Aemon777/chickies-robot/resources/3-d-files/major_parts/monitor mount lasercut v3.step

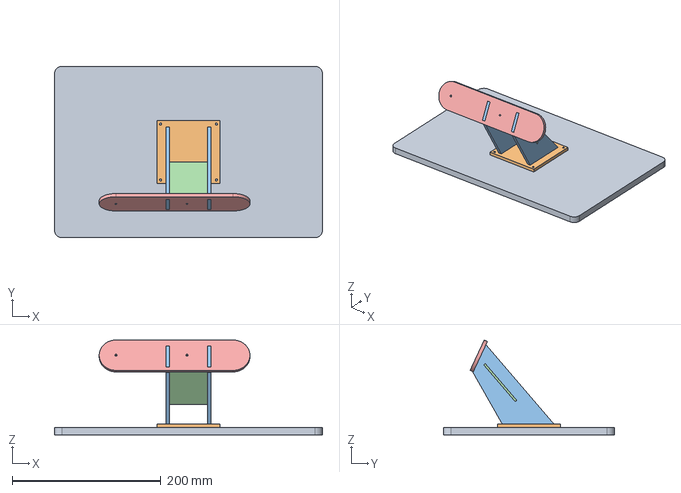
[picture p18: CAD file, 2022-01-21]
resources/3-d-files/major_parts/monitor mount lasercut v3.step
360.0 x 230.0 x 127.6 mm
