Aemon777/chickies-robot/resources/3-d-files/minor_parts/motorcontrollermount v1.step

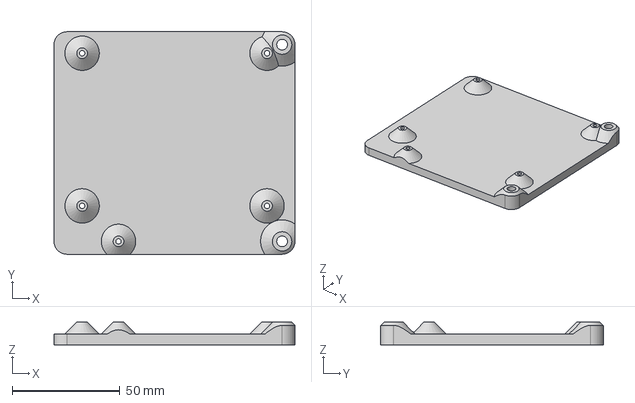
[picture p19: CAD file, 2022-01-21]
resources/3-d-files/minor_parts/motorcontrollermount v1.step
112.1 x 103.5 x 10.5 mm
