Aemon777/chickies-robot/resources/3-d-files/Arm_Models/ChickiesLogo.SLDPRT

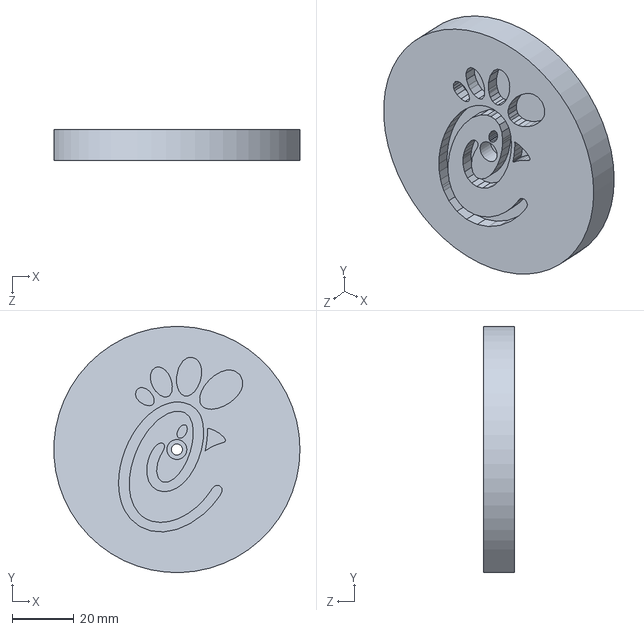
[picture p20: CAD file, 2022-03-17]
resources/3-d-files/Arm_Models/ChickiesLogo.SLDPRT
79.9 x 80.0 x 10.0 mm
