Aemon777/chickies-robot/resources/3-d-files/FCU-Part-Files/Anchor Left.SLDPRT

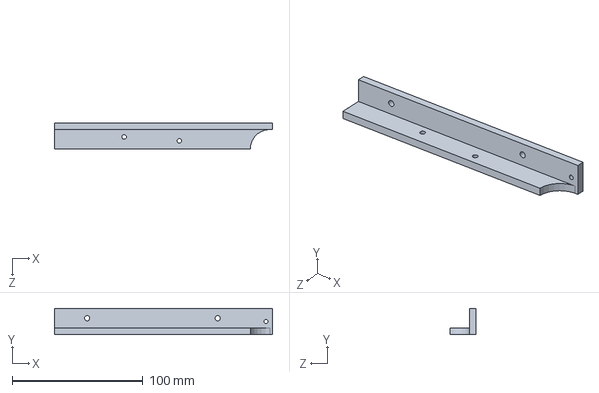
[picture p21: CAD file, 2022-03-31]
resources/3-d-files/FCU-Part-Files/Anchor Left.SLDPRT
167.0 x 20.0 x 20.0 mm
