Aemon777/chickies-robot/resources/3-d-files/minor_parts/powerboardmount v1.step

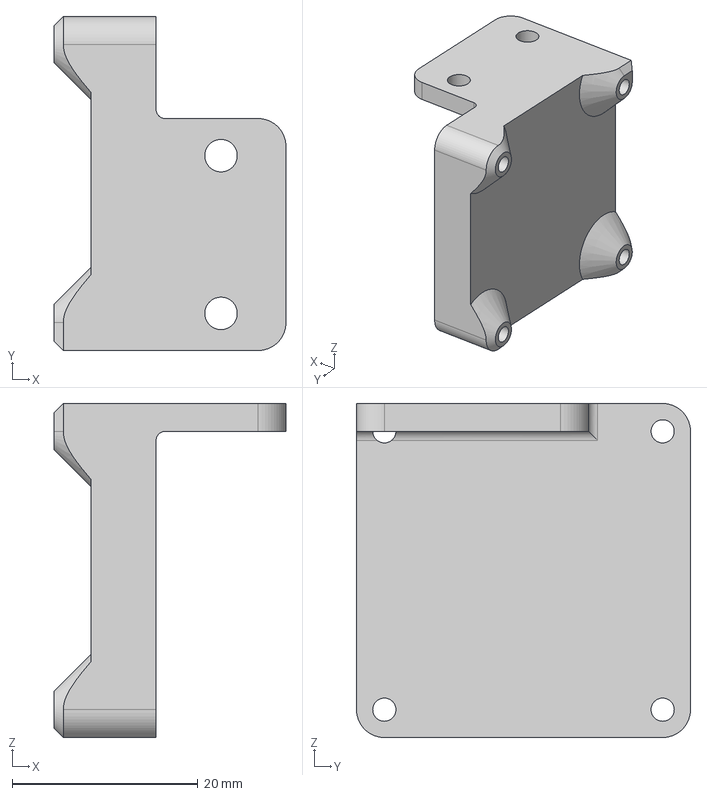
[picture p22: CAD file, 2022-01-21]
resources/3-d-files/minor_parts/powerboardmount v1.step
25.0 x 36.0 x 36.0 mm
