Aemon777/chickies-robot/resources/3-d-files/Arm_Models/Rack Extend.SLDPRT

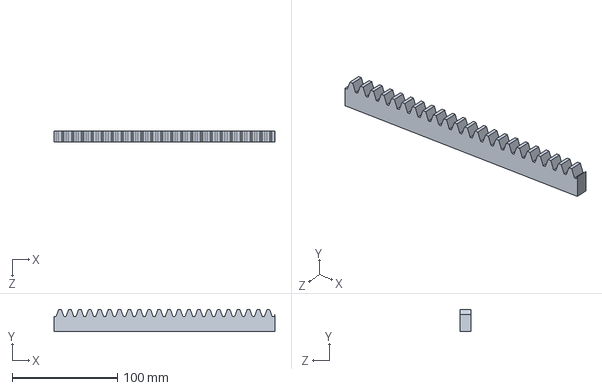
[picture p23: CAD file, 2022-03-17]
resources/3-d-files/Arm_Models/Rack Extend.SLDPRT
210.0 x 21.0 x 10.0 mm
