Aemon777/chickies-robot/resources/3-d-files/major_parts/lidarmount v7.step

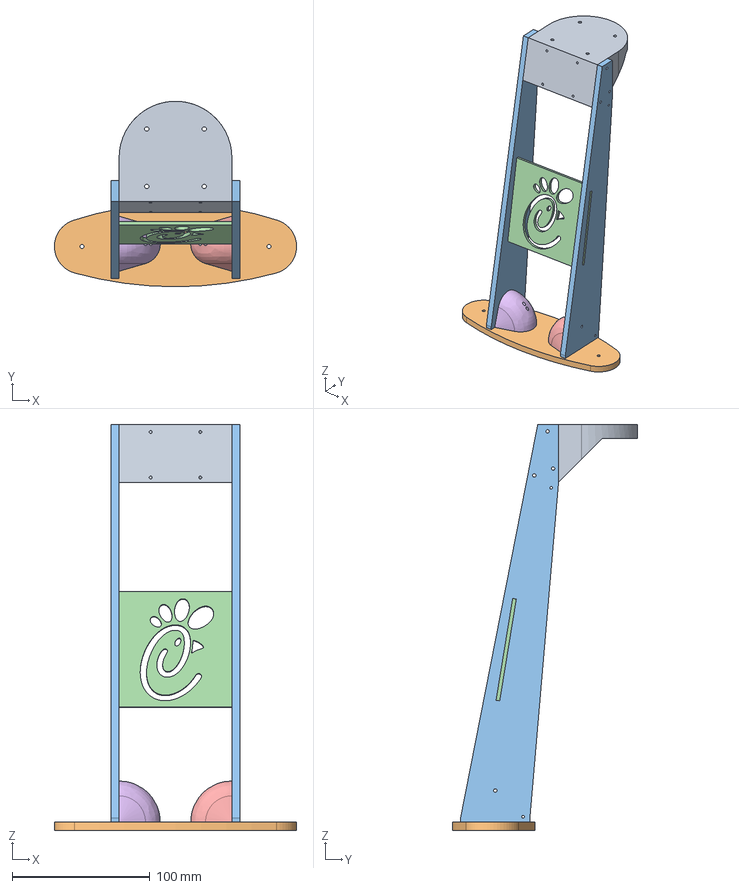
[picture p24: CAD file, 2022-01-21]
resources/3-d-files/major_parts/lidarmount v7.step
176.0 x 134.7 x 295.0 mm
