Aemon777/chickies-robot/resources/3-d-files/minor_parts/knob2 v1.step

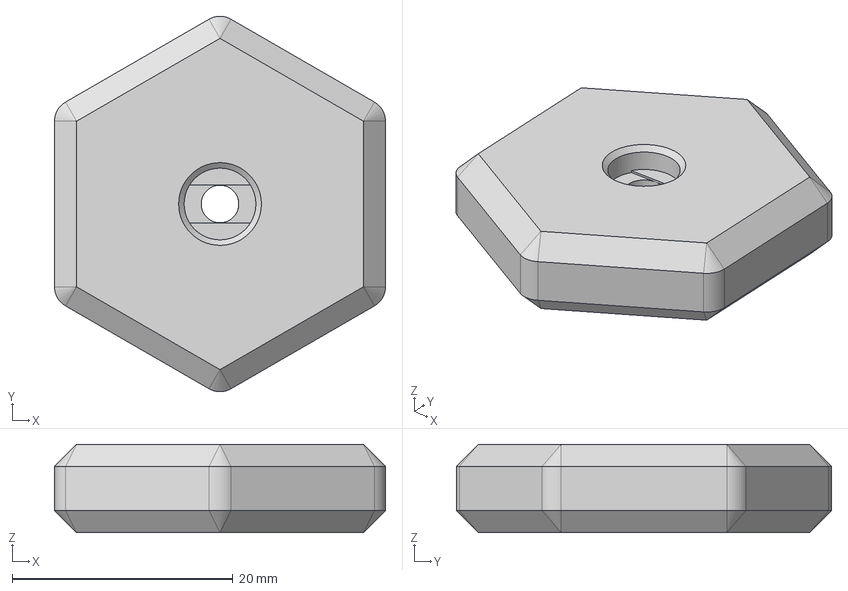
[picture p25: CAD file, 2022-01-21]
resources/3-d-files/minor_parts/knob2 v1.step
30.0 x 34.0 x 8.00 mm
