Aemon777/chickies-robot/resources/3-d-files/FCU-Part-Files/Bottom.SLDPRT

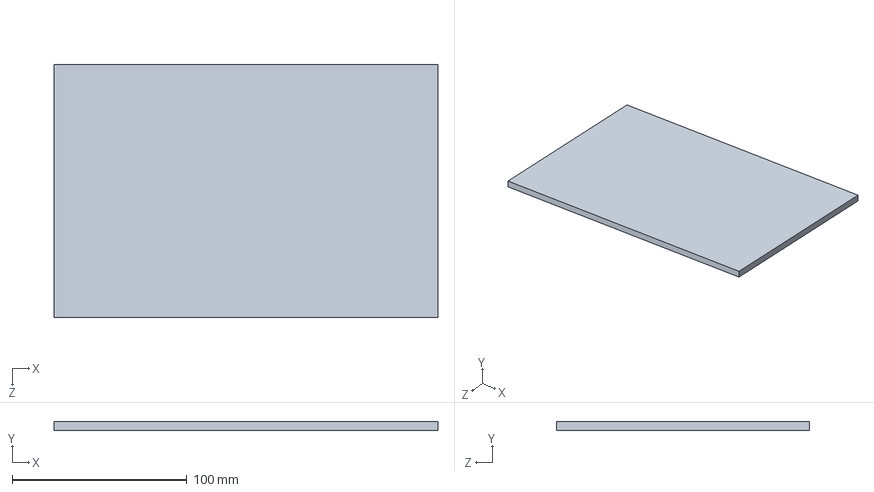
[picture p26: CAD file, 2022-03-31]
resources/3-d-files/FCU-Part-Files/Bottom.SLDPRT
220.0 x 5.00 x 145.0 mm
