Aemon777/chickies-robot/resources/3-d-files/major_parts/monitormounts.dxf

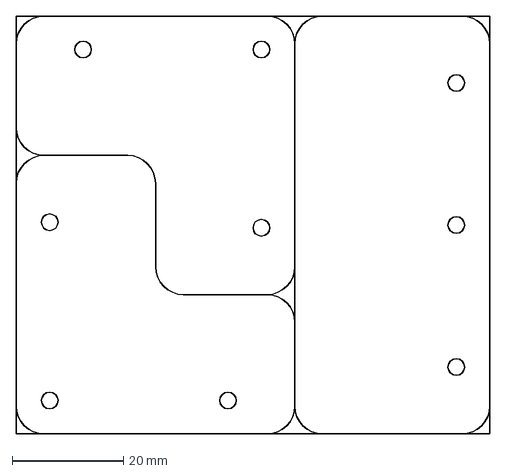
[picture p27: CAD file, 2022-01-21]
resources/3-d-files/major_parts/monitormounts.dxf
85.0 x 75.0 mm
