Aemon777/chickies-robot/resources/3-d-files/minor_parts/batterypacking v2.step

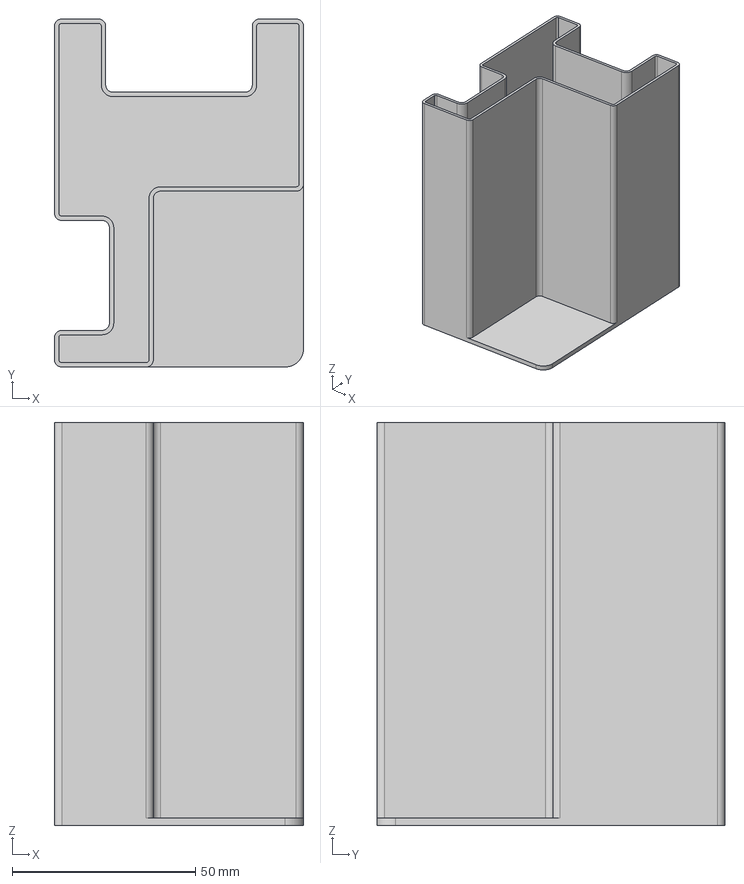
[picture p28: CAD file, 2022-01-21]
resources/3-d-files/minor_parts/batterypacking v2.step
68.0 x 95.0 x 110.0 mm
