Aemon777/chickies-robot/resources/3-d-files/Arm_Models/Gear v1.SLDPRT

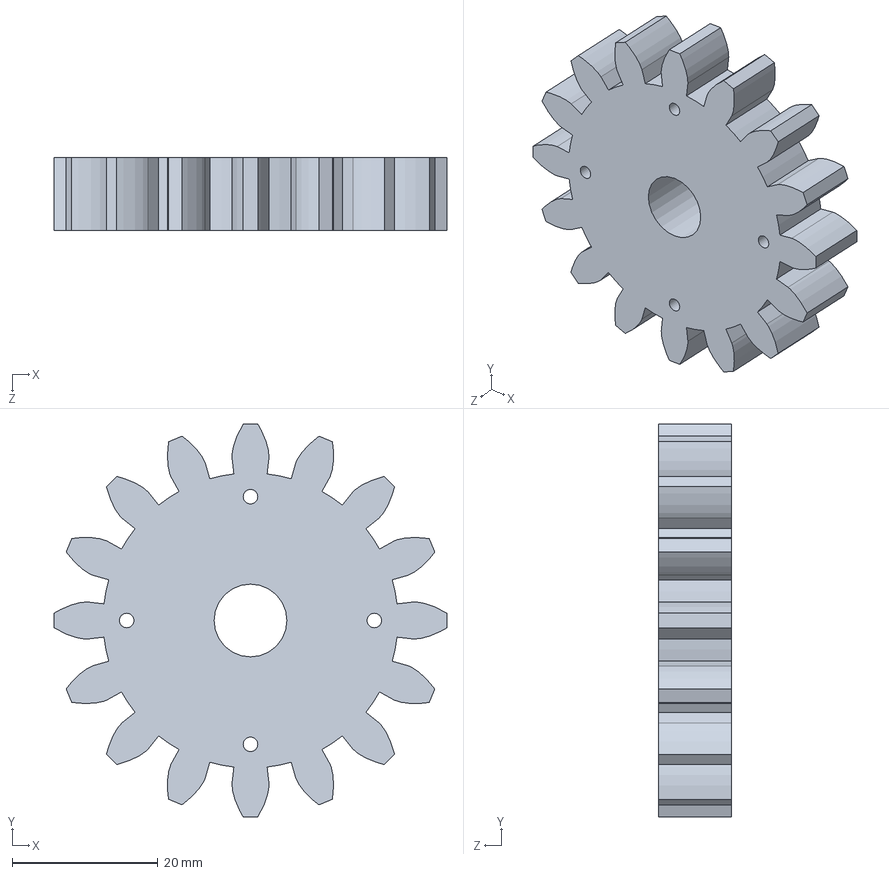
[picture p29: CAD file, 2022-03-17]
resources/3-d-files/Arm_Models/Gear v1.SLDPRT
54.0 x 54.0 x 10.0 mm
