Aemon777/chickies-robot/resources/3-d-files/FCU-Part-Files/Front Door.SLDPRT

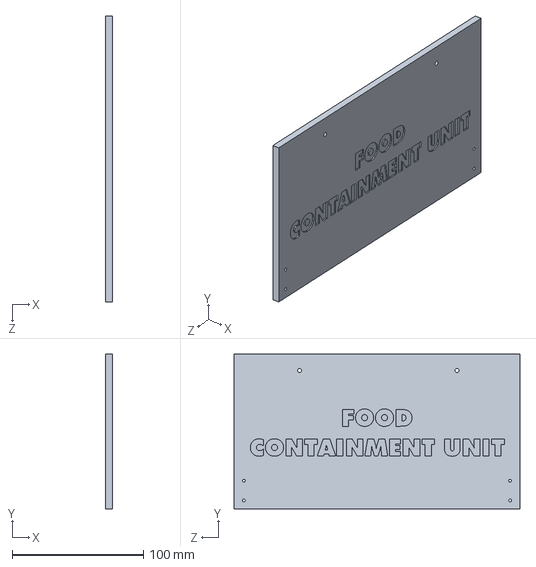
[picture p30: CAD file, 2022-03-31]
resources/3-d-files/FCU-Part-Files/Front Door.SLDPRT
5.00 x 118.0 x 218.0 mm
