Aemon777/chickies-robot/resources/3-d-files/Arm_Models/Servo Futaba S3003.SLDPRT

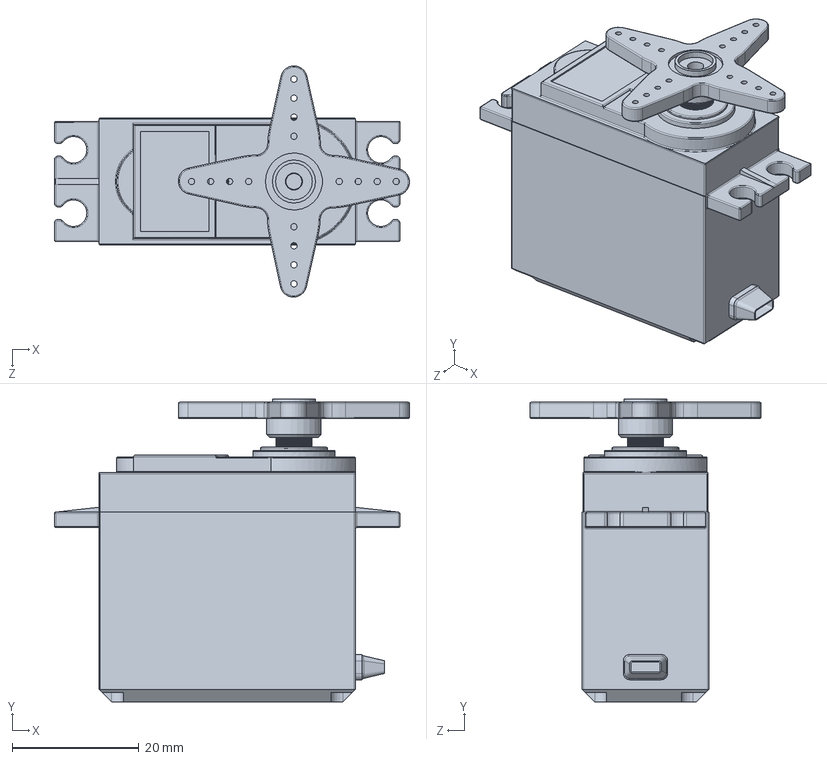
[picture p31: CAD file, 2022-03-17]
resources/3-d-files/Arm_Models/Servo Futaba S3003.SLDPRT
56.0 x 47.8 x 36.5 mm
