Aemon777/chickies-robot/resources/3-d-files/FCU-Part-Files/Handle.SLDPRT

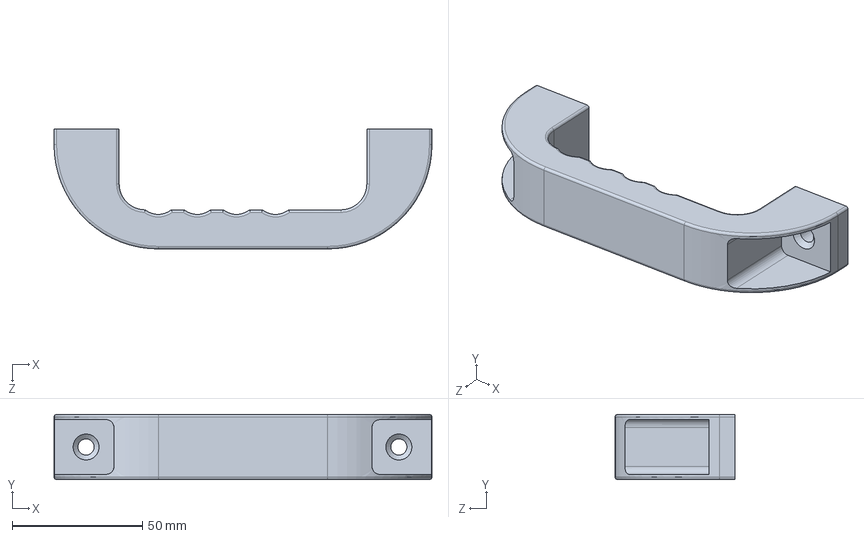
[picture p32: CAD file, 2022-03-31]
resources/3-d-files/FCU-Part-Files/Handle.SLDPRT
145.0 x 25.0 x 46.0 mm
