Aemon777/chickies-robot/resources/3-d-files/Arm_Models/Servo Holder.SLDPRT

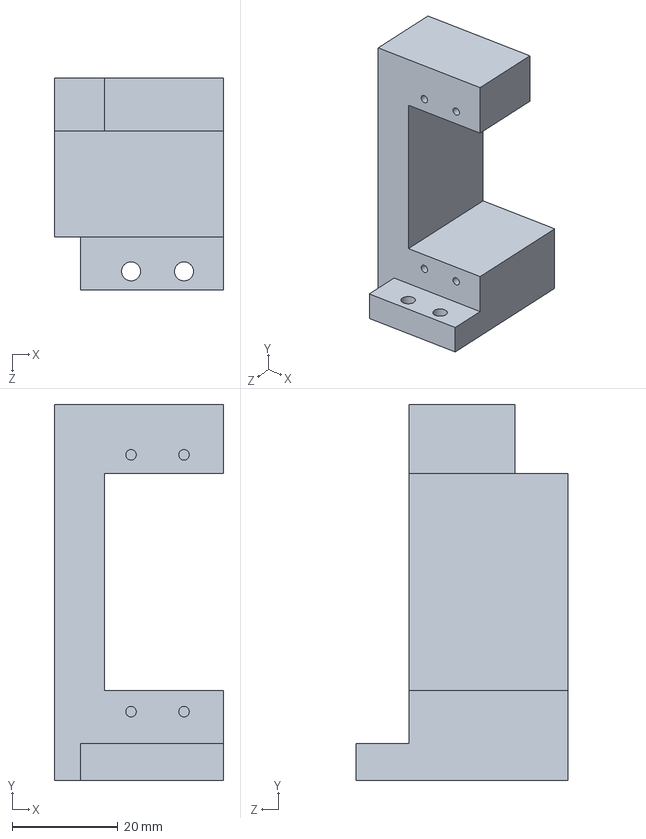
[picture p33: CAD file, 2022-03-17]
resources/3-d-files/Arm_Models/Servo Holder.SLDPRT
32.0 x 71.0 x 40.0 mm
