Aemon777/chickies-robot/resources/3-d-files/FCU-Part-Files/Back-side bracket.SLDPRT

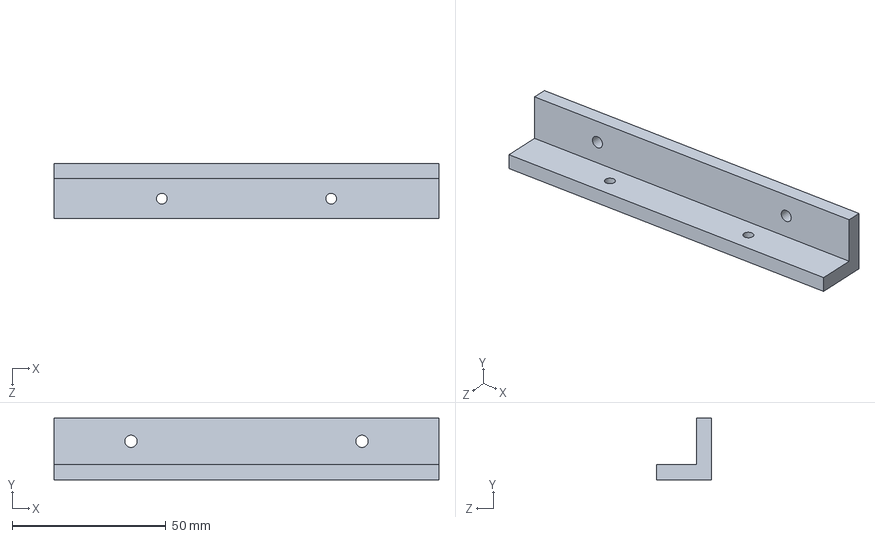
[picture p34: CAD file, 2022-03-31]
resources/3-d-files/FCU-Part-Files/Back-side bracket.SLDPRT
125.0 x 20.0 x 18.0 mm
