Aemon777/chickies-robot/resources/3-d-files/Arm_Models/BeefyServo.SLDPRT

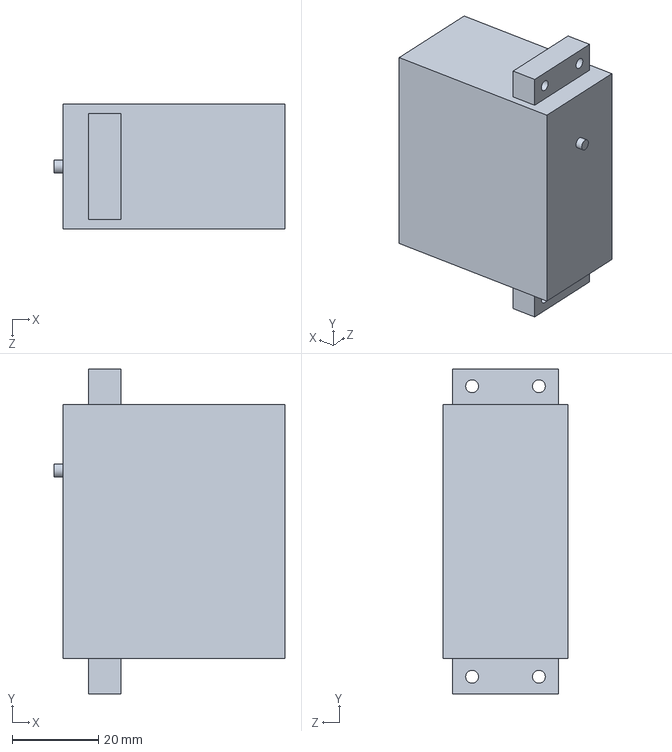
[picture p35: CAD file, 2022-03-14]
resources/3-d-files/Arm_Models/BeefyServo.SLDPRT
53.5 x 75.4 x 29.0 mm
