Aemon777/chickies-robot/resources/3-d-files/Arm_Models/limiters_made.SLDPRT

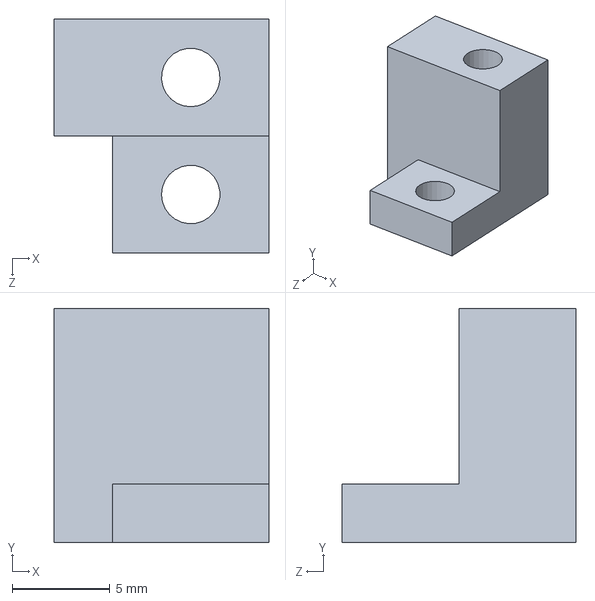
[picture p36: CAD file, 2022-03-14]
resources/3-d-files/Arm_Models/limiters_made.SLDPRT
11.0 x 12.0 x 12.0 mm
