Aemon777/chickies-robot/resources/3-d-files/FCU-Part-Files/Back Wall.SLDPRT

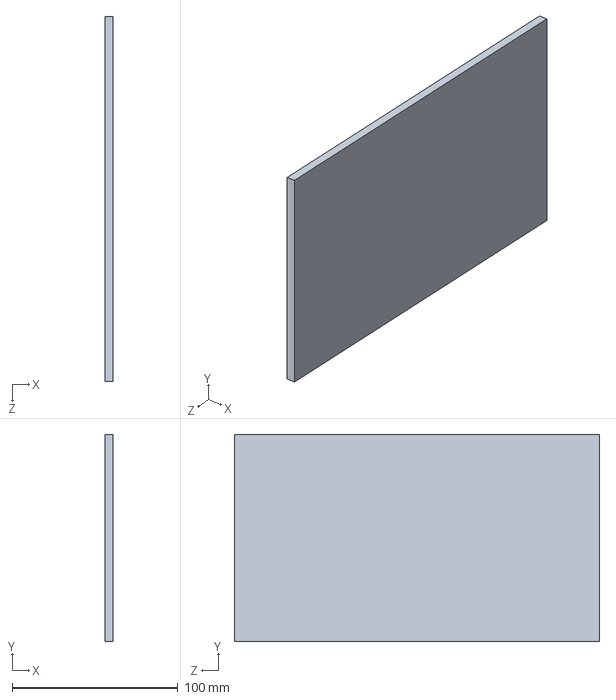
[picture p37: CAD file, 2022-03-31]
resources/3-d-files/FCU-Part-Files/Back Wall.SLDPRT
5.00 x 125.0 x 220.0 mm
