Aemon777/chickies-robot/resources/3-d-files/FCU-Part-Files/Top.SLDPRT

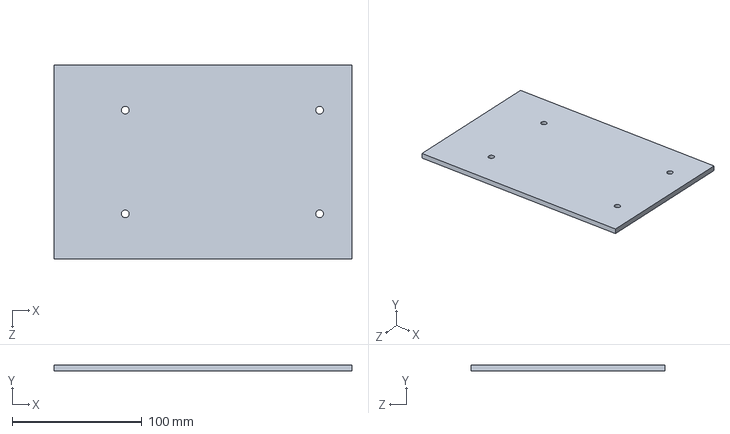
[picture p38: CAD file, 2022-03-31]
resources/3-d-files/FCU-Part-Files/Top.SLDPRT
230.0 x 5.00 x 150.0 mm
