Aemon777/chickies-robot/resources/3-d-files/Arm_Models/LimitSwitch.SLDPRT

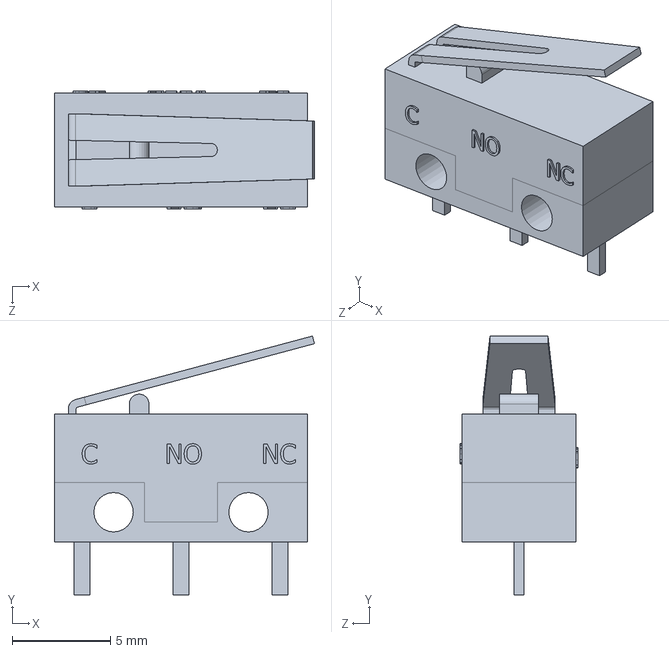
[picture p39: CAD file, 2022-03-14]
resources/3-d-files/Arm_Models/LimitSwitch.SLDPRT
13.2 x 13.1 x 6.00 mm
