Aemon777/chickies-robot/resources/3-d-files/FCU-Part-Files/Magnet Holder.SLDPRT

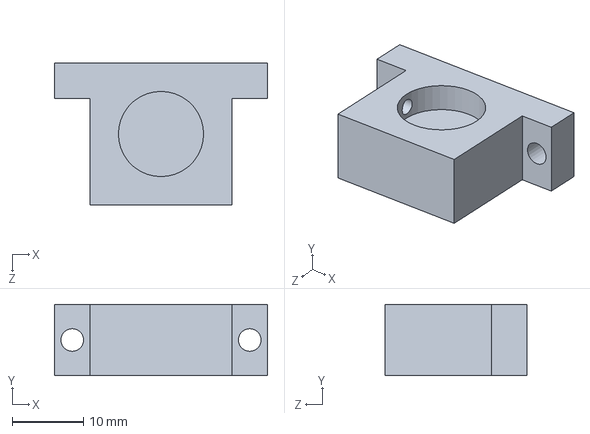
[picture p40: CAD file, 2022-03-31]
resources/3-d-files/FCU-Part-Files/Magnet Holder.SLDPRT
30.0 x 10.0 x 20.0 mm
