Aemon777/chickies-robot/resources/3-d-files/Arm_Models/slider_made.SLDPRT

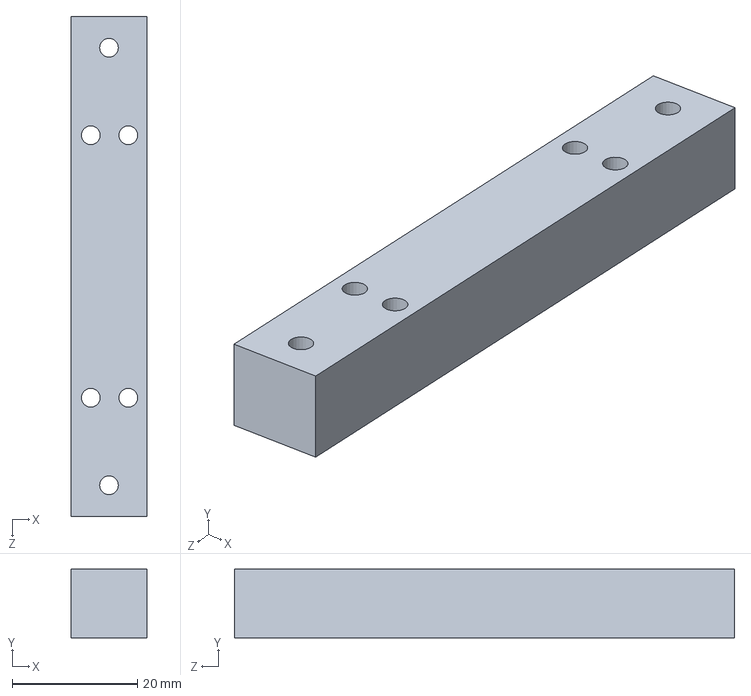
[picture p41: CAD file, 2022-03-14]
resources/3-d-files/Arm_Models/slider_made.SLDPRT
12.2 x 11.0 x 80.0 mm
