Aemon777/chickies-robot/resources/3-d-files/FCU-Part-Files/Side Wall.SLDPRT

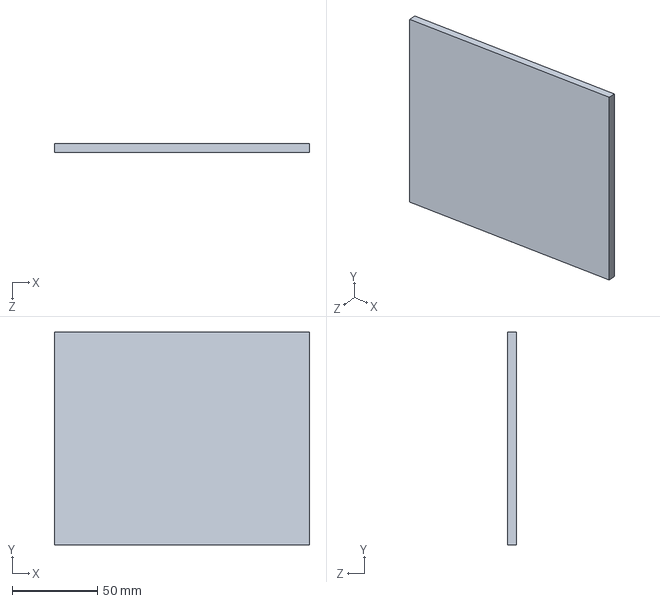
[picture p42: CAD file, 2022-03-31]
resources/3-d-files/FCU-Part-Files/Side Wall.SLDPRT
150.0 x 125.0 x 5.00 mm
