Aemon777/chickies-robot/resources/3-d-files/Arm_Models/limit_stand.SLDPRT

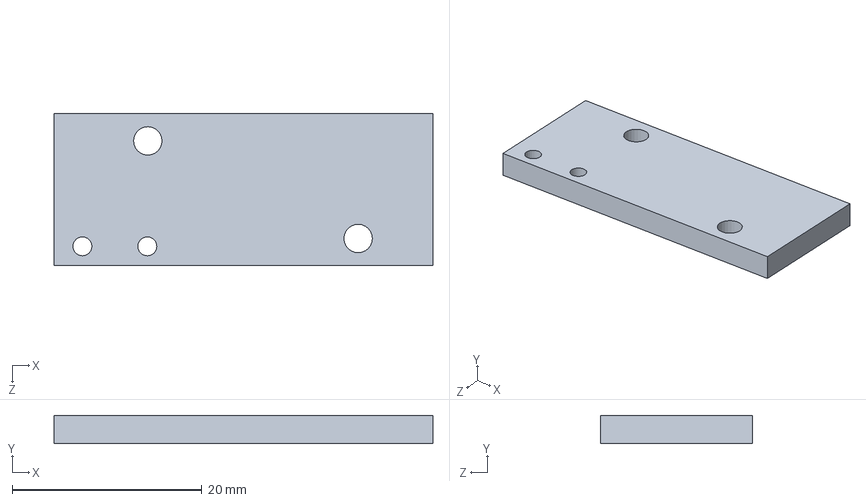
[picture p43: CAD file, 2022-03-14]
resources/3-d-files/Arm_Models/limit_stand.SLDPRT
40.0 x 3.00 x 16.0 mm
