Aemon777/chickies-robot/resources/3-d-files/Arm_Models/BeefyHolder.SLDPRT

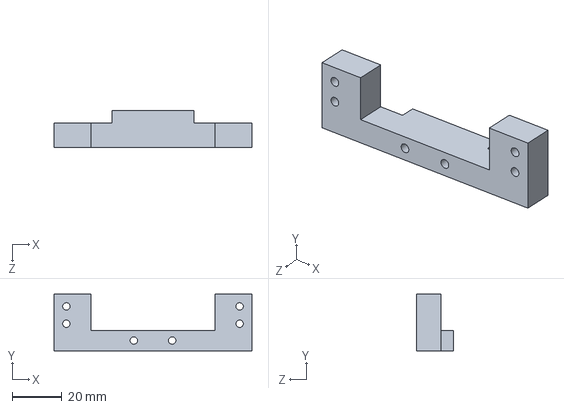
[picture p44: CAD file, 2022-03-14]
resources/3-d-files/Arm_Models/BeefyHolder.SLDPRT
80.0 x 23.0 x 15.0 mm
