Aemon777/chickies-robot/playground/newSmoothDrive.py

#This program implements drive functions using gpiozero with the intent of
#receiving commands from a Flysky FS-i6 remote. The throttle is managed
#by the left stick, turns by the right stick. Two switches are used: the 
#left switch is up:forward/down:reverse. The second from the right is
#up:normal/middle:half-speed/down:stop.

import serial
import gpiozero as gpio
from time import sleep
import yaml

with open("/home/ubuntu/chickies-robot/resources/comports.yaml", "r") as stream:
    try:
        data = yaml.safe_load(stream)
        serialPort=serial.Serial(data['RADIO_PORT'],data['RADIO_BAUDRATE'])
    except yaml.YAMLError as exc:
        print(exc)

#These are the motor variables. *Dir.on() sets direction forward, *Dir.off() backward
#*Pwm.value = <pwm between 0 and 1>
leftPwm = gpio.PWMLED(13)
leftDir = gpio.LED(6)
rightPwm = gpio.PWMLED(12)
rightDir = gpio.LED(5)

leftVal = 0.00
rightVal = 0.00
n = True

while n:
    try:
        read = serialPort.readline().decode('utf-8')
        data = read.split(',')
        throttle = int(data[2])
        steering = int(data[0])
        secondaryThrottle = int(data[1])
        secondarySteering = int(data[3])
        reverse = (int(data[4]) > 50)
        maxPwm = 100 - int(data[5])

        if reverse:
            throttle = -throttle
        
        speedModifier = throttle
        leftModifier = int(steering*1.5) - 75
        rightModifier = -leftModifier
        left = speedModifier + leftModifier
        right = speedModifier + rightModifier
        
        if left > 100:
            left = 100
        if left < -100:
            left = -100
        if right > 100:
            right = 100
        if left < -100:
            left = -100

        left = left*maxPwm/100
        right = right*maxPwm/100

        leftVal = round(0.75*leftVal + 0.25*left)
        rightVal = round(0.75*rightVal + 0.25*right)
        
        if leftVal <= 2 and leftVal >= -2:
            leftVal = 0
        if rightVal <= 2 and rightVal >= -2:
            rightVal = 0

        if leftVal < 0 and leftDir.is_active:
            leftDir.off()
        elif leftVal > 0 and not leftDir.is_active:
            leftDir.on()
        if rightVal < 0 and rightDir.is_active:
            rightDir.off()
        elif rightVal > 0 and not rightDir.is_active:
            rightDir.on()

        if leftPwm.value != abs(leftVal/100.00):
            leftPwm.value = abs(leftVal/100.00)
        if rightPwm.value != abs(rightVal/100.00):
            rightPwm.value = abs(rightVal/100.00)
        
        print(leftVal,rightVal)
            
    except KeyboardInterrupt:
        n = False
        
serialPort.close()
