Aemon777/chickies-robot/catkin_ws/src/motor_controller/scripts/radio_receiver.py

#!/usr/bin/env/python

import rospy
from std_msgs.msg import String
from geometry_msgs.msg import Twist
import serial
import yaml

class radio_receiver():
    def __init__(self):
        with open("/home/ubuntu/chickies-robot/resources/comports.yaml", "r") as stream:
            try:
                data = yaml.safe_load(stream)
                self.serialPort = serial.Serial(data['RADIO_PORT'],data['RADIO_BAUDRATE'])
            except yaml.YAMLError as exc:
                print(exc)
        self.pub_vel = rospy.Publisher('cmd_vel', Twist, queue_size = 10)
        rospy.init_node('radio_receiver', anonymous=True)
        self.rate = rospy.Rate(50)
        self.errorCount = 0

    def spin(self):
        while not rospy.is_shutdown():
            self.spinOnce()
            self.rate.sleep()
    
    def spinOnce(self):
        #read from port
        read = ""
        data = list()
        read = self.serialPort.readline().decode('utf-8')
        data = read.split(',')
        if len(data) > 5:
            print(read)
            data = read.split(',')
            #twist/velocity message
            for_rev = (int(data[4]) < 50)
            throttle = int(data[2])
            steer = -1 if int(data[0]) == 0 else int(data[0])
            steerLeft = -1*(steer)*1.5 + 75
            vel = Twist()
            vel.linear.x = throttle*1.25/200
            if not for_rev:
                vel.linear.x = -vel.linear.x
            vel.angular.z = steerLeft/75
            rospy.loginfo(vel)
            self.pub_vel.publish(vel)
        else:
           self.errorCount += 1
           if self.errorCount % 10 == 0:
                print(self.errorCount)

if __name__ == '__main__':
    try:
        radio_receiver = radio_receiver()
        radio_receiver.spin()
    except rospy.ROSInterruptException:
        pass
