Aemon777/chickies-robot/resources/Adafruit_CircuitPython_Nunchuk/nunchuk_simpletest.py

# SPDX-FileCopyrightText: 2021 ladyada for Adafruit Industries
# SPDX-License-Identifier: MIT

import time
import board
import adafruit_nunchuk

nc = adafruit_nunchuk.Nunchuk(board.I2C())

while True:
    x, y = nc.joystick
    ax, ay, az = nc.acceleration
    print("joystick = {},{}".format(x, y))
    print("acceleration ax={}, ay={}, az={}".format(ax, ay, az))

    if nc.buttons.C:
        print("button C")
    if nc.buttons.Z:
        print("button Z")
    time.sleep(0.5)
